danielkummer/infoDome/3d workfiles/clock hand.stl

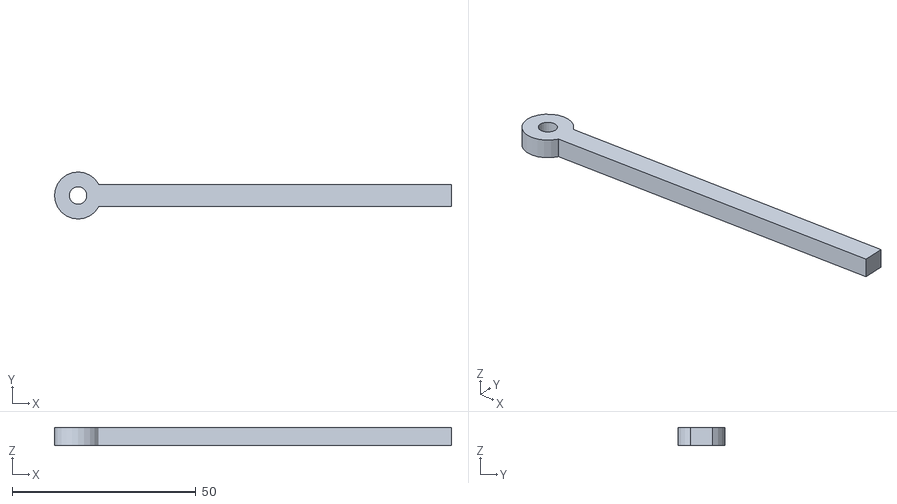
[picture p28: CAD file, 2017-03-26]
3d workfiles/clock hand.stl
108.2 x 12.8 x 5.00
