danielkummer/infoDome/3d workfiles/tubewithservo.stl

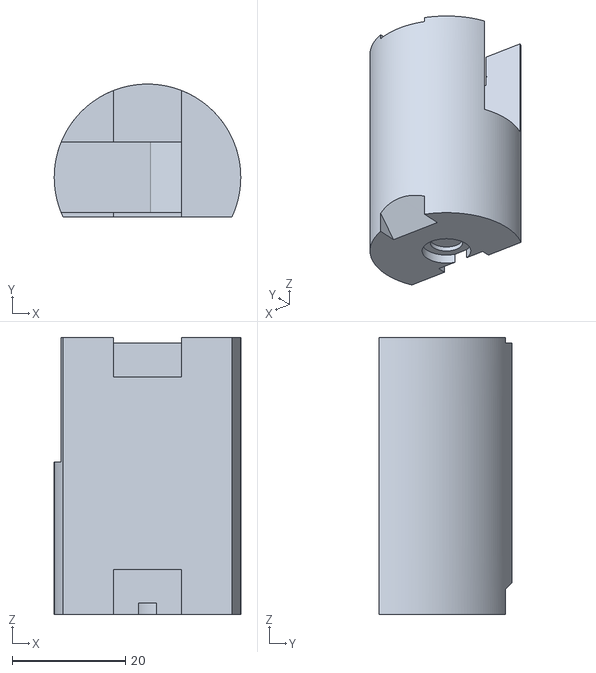
[picture p30: CAD file, 2017-03-26]
3d workfiles/tubewithservo.stl
33.0 x 23.5 x 49.0
