danielkummer/infoDome/3d print/state icons/Infodome States (all).stl

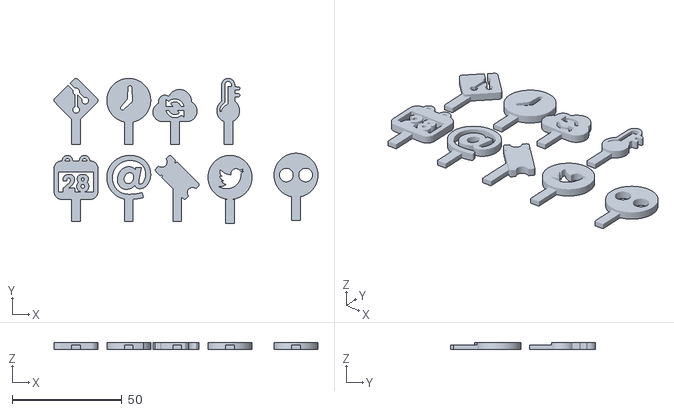
[picture p31: CAD file, 2017-03-26]
3d print/state icons/Infodome States (all).stl
120.0 x 66.0 x 3.00
