danielkummer/infoDome/3d workfiles/final_tube (repaired).stl

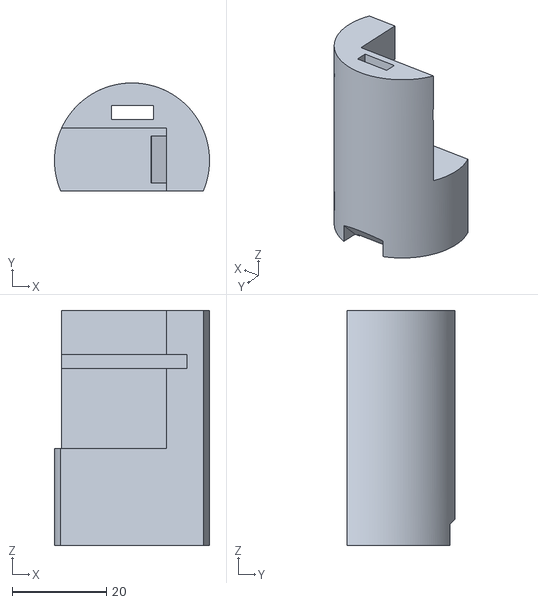
[picture p32: CAD file, 2017-03-26]
3d workfiles/final_tube (repaired).stl
33.0 x 23.0 x 50.0
