danielkummer/infoDome/3d print/state icons/date_state.stl

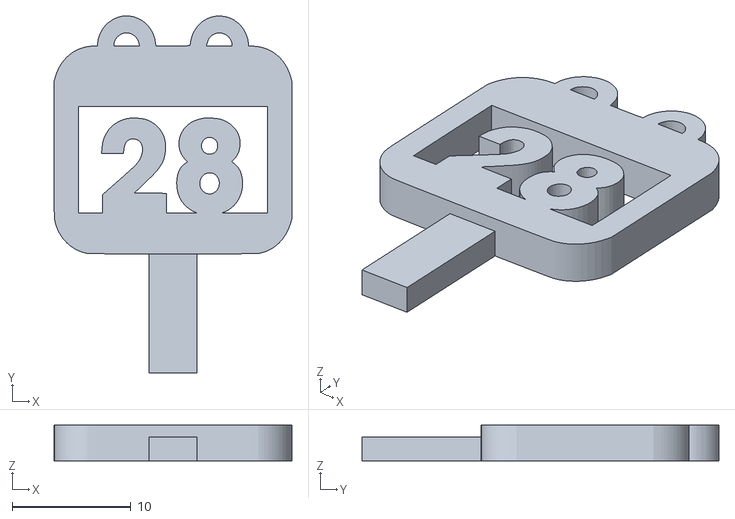
[picture p34: CAD file, 2017-03-26]
3d print/state icons/date_state.stl
20.0 x 30.0 x 3.00
