danielkummer/infoDome/3d workfiles/topplug.stl

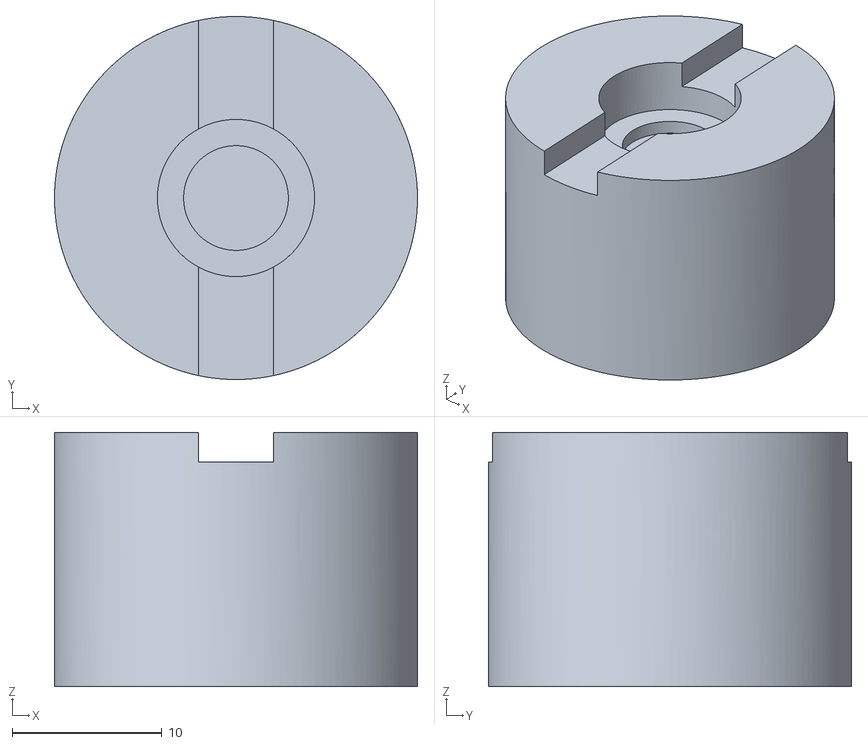
[picture p35: CAD file, 2016-01-03]
3d workfiles/topplug.stl
24.3 x 24.3 x 17.0
