danielkummer/infoDome/3d workfiles/middleplug.stl

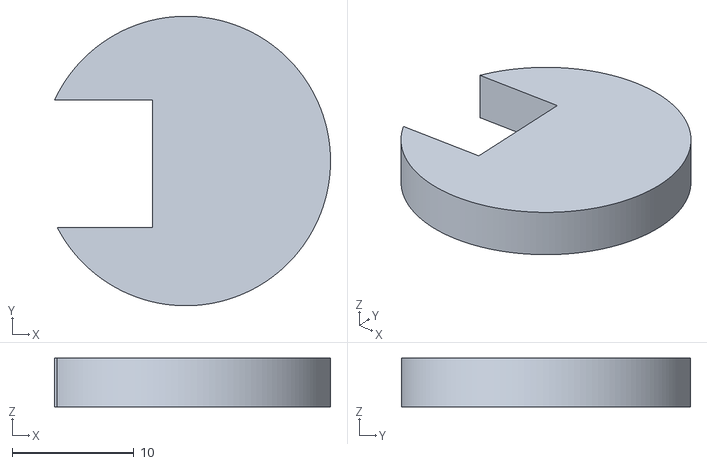
[picture p36: CAD file, 2016-01-03]
3d workfiles/middleplug.stl
22.6 x 23.7 x 4.00
